karl-mohring/Lurker/Code/OfficeLurker/Thingspeak.py

import json

thingspeakMapping = {
    "airTemp" = "field1",
    "surfaceTemp" = "field2",
    "humidity" = "field3",
    "illuminance" = "field4",
    "noiseLevel" = "field5",
    "motion" = "field6"
}
